LeovR/ableton-midi-foot-controller/Button.h

#ifndef Button_h
#define Button_h

#include <Bounce2.h>
#include "Arduino.h"

class Button {
  public:
    // Class Variable


    // Public Attributes


    // Constructors
    Button();

    // Destructors
    ~Button();

    // Public functions
    boolean update();
    void init(byte pin);
    void init(byte pin, byte led);
    boolean isPressed();
    boolean isJustPressed();
    boolean isJustReleased();
    byte getPin();
    void turnLedOn();
    void turnLedOff();
    boolean isLedTurnedOn();

  private:
    // Private Attributes
    byte _pin;
    byte _led;
    Bounce _button;
    byte _previousState;
    boolean _justReleased;
    boolean _justPressed;
    boolean _pressed;
    boolean _ledOn;
    // Private Functions


};



#endif
